IktaS/Pill60/Case/CasePlate-1,5mm.dxf

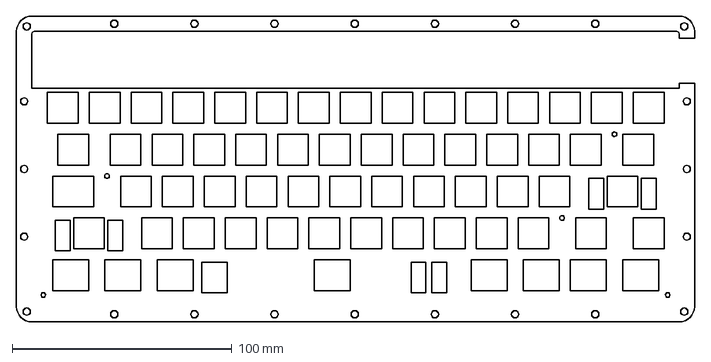
[picture p20: CAD file, 2021-05-22]
Case/CasePlate-1,5mm.dxf
308.7 x 139.2 mm
